lord-feistel/hardware_hacking_lab/images_videos/connection_ISP_atmel.jpeg

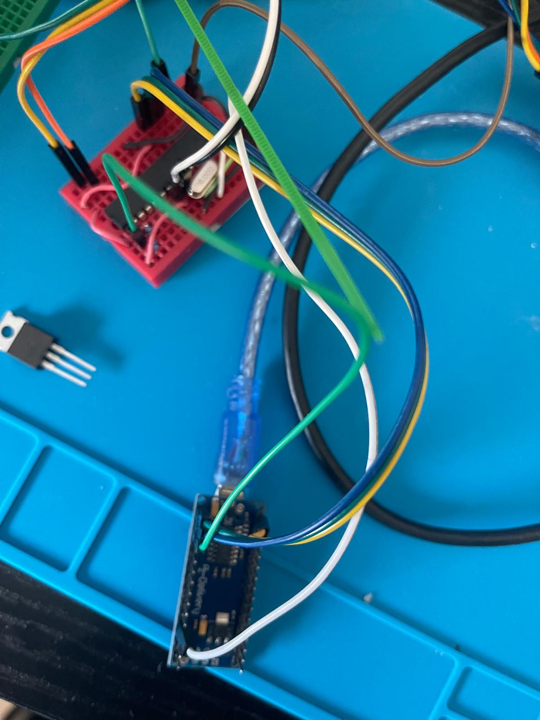
images_videos/connection_ISP_atmel.jpeg
