lord-feistel/hardware_hacking_lab/images_videos/normally_working.PNG

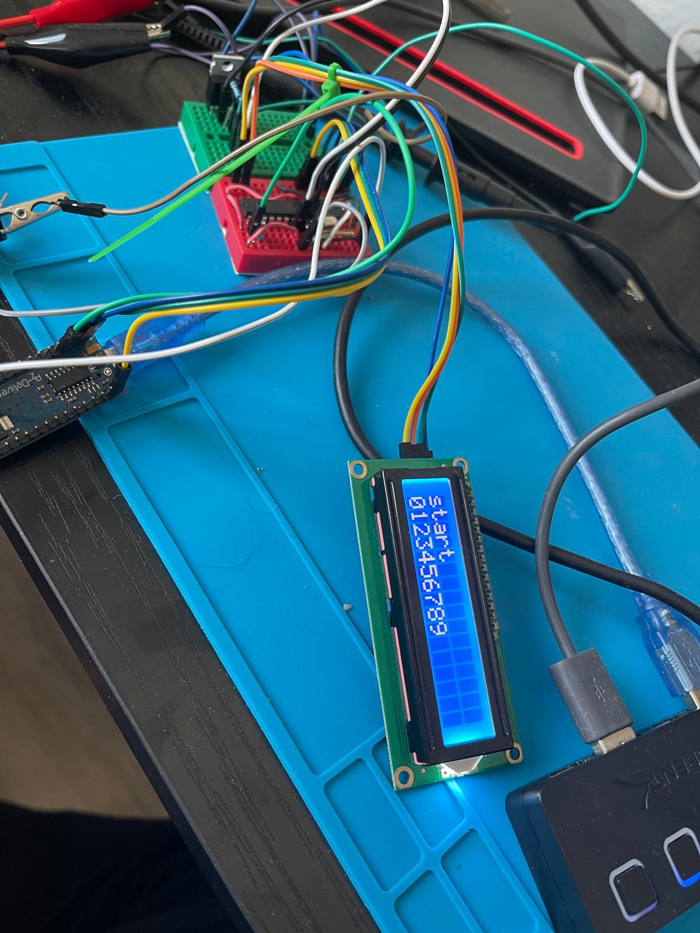
images_videos/normally_working.PNG
