lord-feistel/hardware_hacking_lab/hardware/arduino_glitching/arduino_glitching.kicad_sch

## KiCad design hardware/arduino_glitching/arduino_glitching.kicad_sch (2024-05-03)

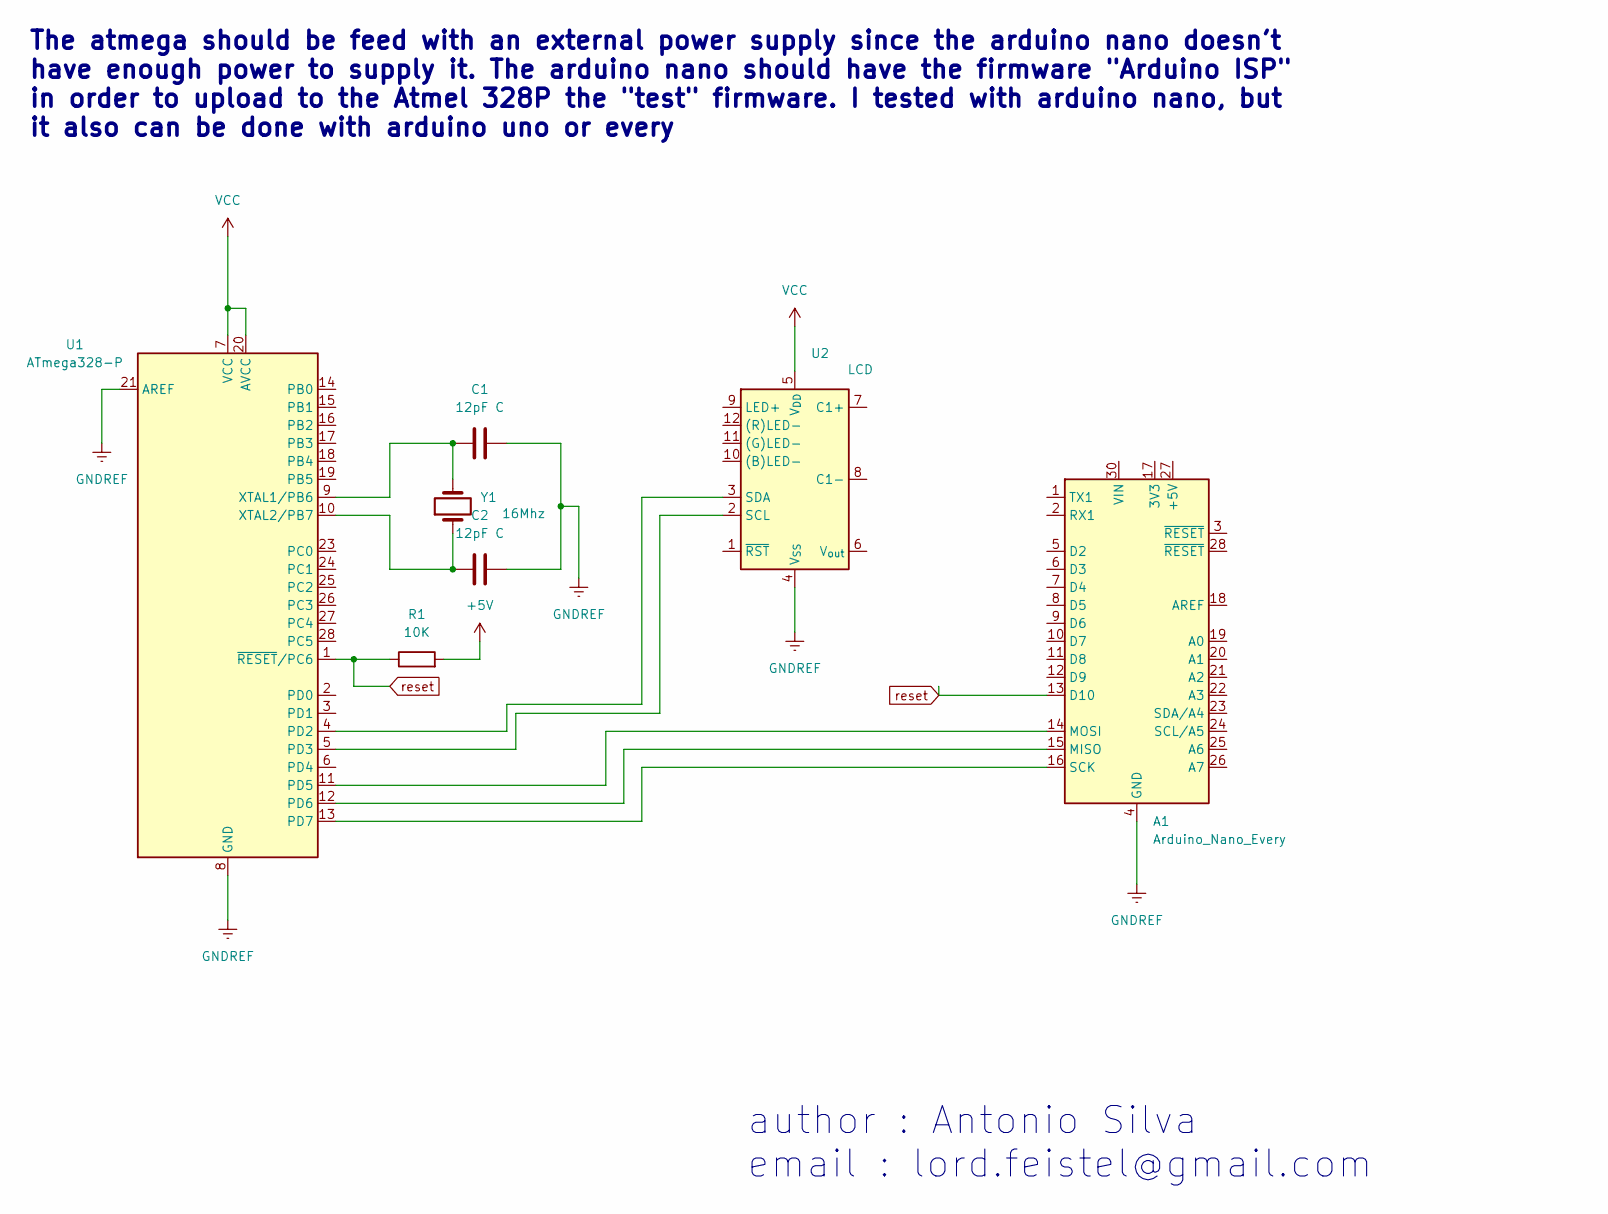
[picture p29: schematic arduino_glitching.kicad_sch]

Parts:
A1: Arduino_Nano_Every; Arduino_Nano
C1, C2: 12pF C
R1: 10K
U1: ATmega328-P; DIP-28_W7.62mm
U2: LCD; NHD-C0220BiZ-FSRGB
Y1: 16Mhz

Connections:
+5V: R1.2
GNDREF: A1.4 (GND), A1.29 (GND), C1.2, C2.2, U1.8 (GND), U1.21 (AREF), U1.22 (GND), U2.4 (V_{SS})
unnamed: A1.14 (MOSI), U1.11 (PD5)
unnamed: A1.15 (MISO), U1.12 (PD6)
unnamed: A1.16 (SCK), U1.13 (PD7)
unnamed: C1.1, U1.9 (XTAL1/PB6), Y1.2
unnamed: C2.1, U1.10 (XTAL2/PB7), Y1.1
unnamed: U1.4 (PD2), U2.3 (SDA)
unnamed: U1.5 (PD3), U2.2 (SCL)
VCC: U1.7 (VCC), U1.20 (AVCC), U2.5 (V_{DD})
reset: A1.13 (D10), R1.1, U1.1 (~RESET/PC6)

Notes on the sheet:
The atmega should be feed with an external power supply since the arduino nano doesn't have enough power to supply it. The arduino nano should have the firmware "Arduino ISP" in order to upload to the Atmel 328P the "test" firmware. I tested with arduino nano, but it also can be done with arduino u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
author : Antonio Silva email : lord.feistel@gmail.com
