lord-feistel/hardware_hacking_lab/hardware/arduino_glitching/arduino_mosfet/arduino_mosfet.kicad_sch

## KiCad design hardware/arduino_glitching/arduino_mosfet/arduino_mosfet.kicad_sch (2024-05-03)

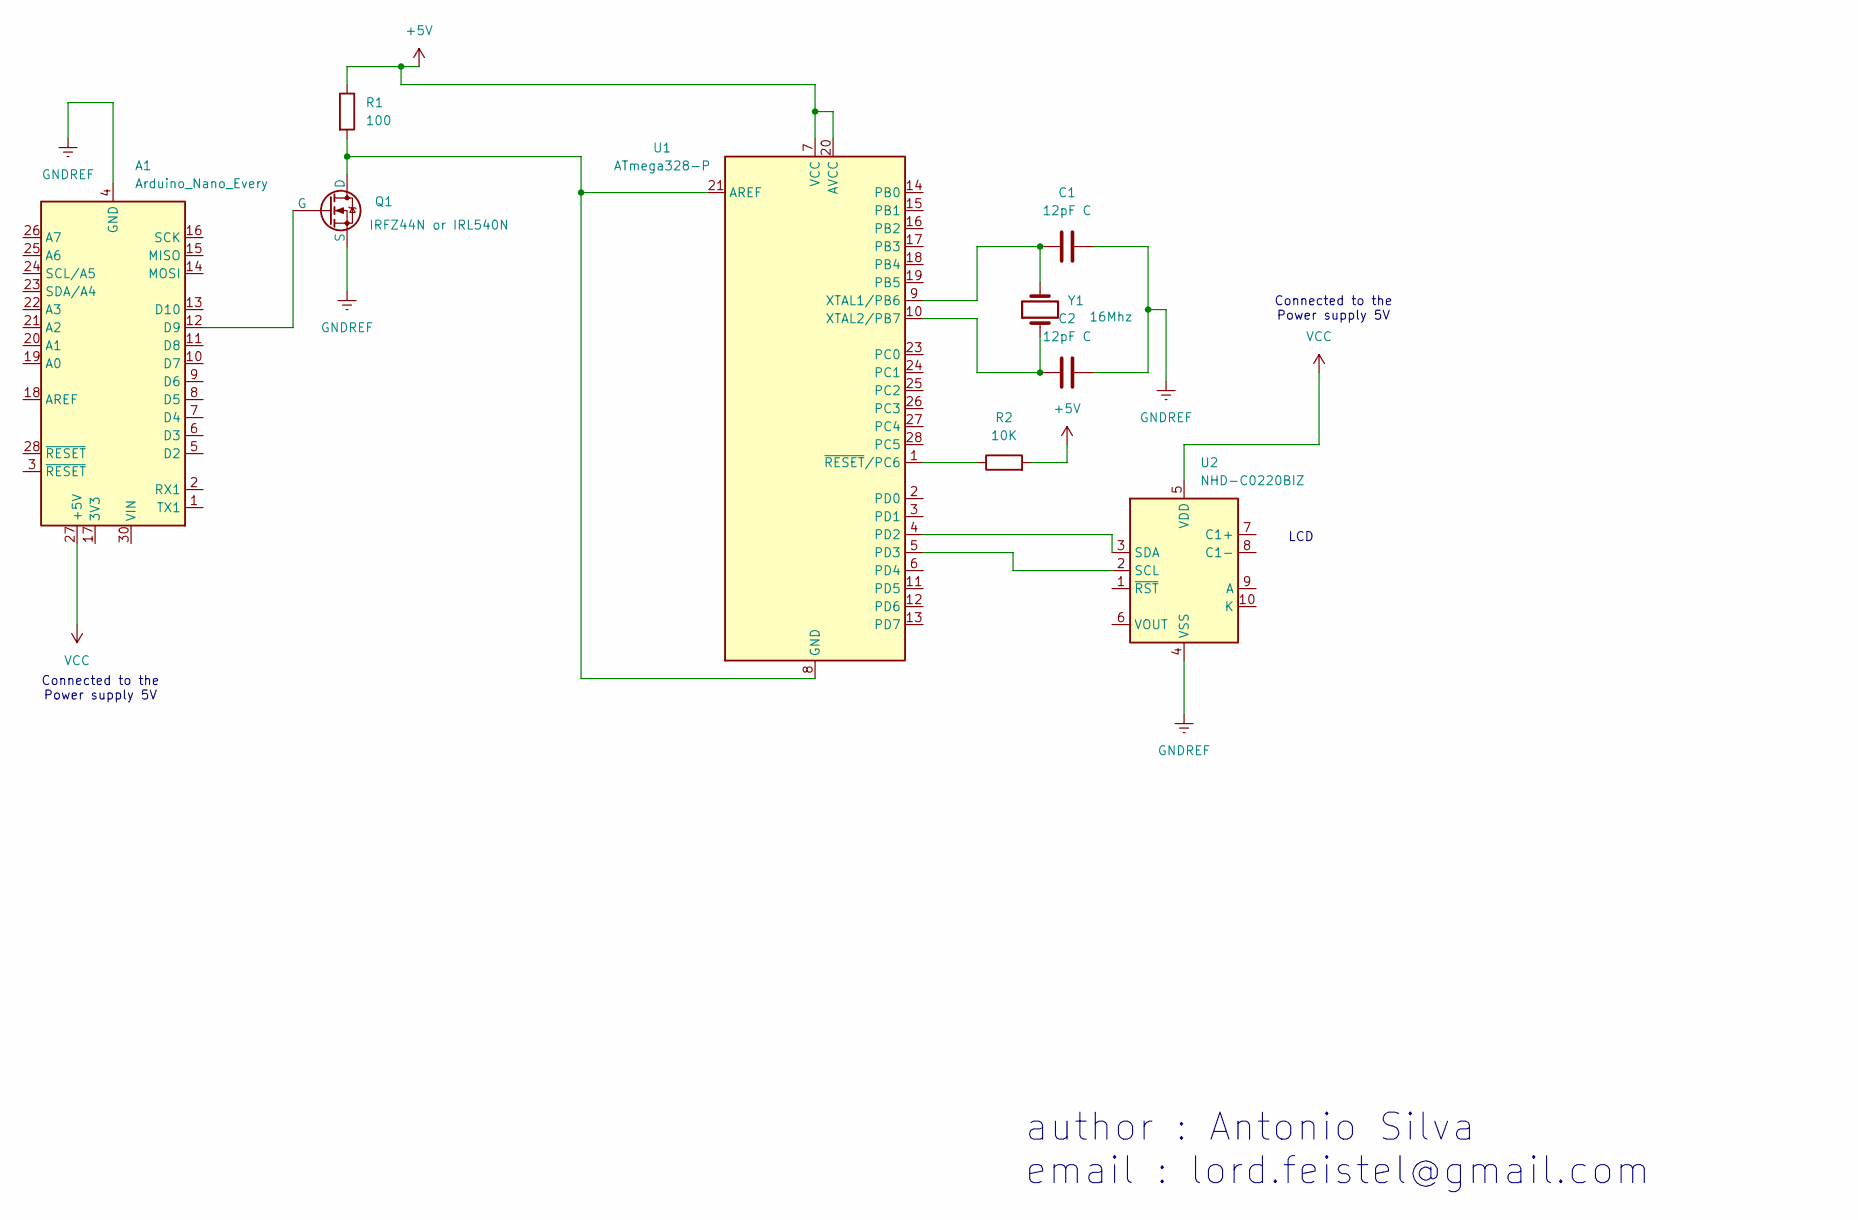
[picture p30: schematic arduino_mosfet.kicad_sch]

Parts:
A1: Arduino_Nano_Every; Arduino_Nano
C1, C2: 12pF C
Q1: IRFZ44N or IRL540N
R1: 100
R2: 10K
U1: ATmega328-P; DIP-28_W7.62mm
U2: NHD-C0220BIZ; NHD-C0220BiZ
Y1: 16Mhz

Connections:
+5V: R1.1, R2.2, U1.7 (VCC), U1.20 (AVCC)
GNDREF: A1.4 (GND), A1.29 (GND), C1.2, C2.2, Q1.3 (S), U2.4 (VSS)
unnamed: A1.12 (D9), Q1.2 (G)
unnamed: C1.1, U1.9 (XTAL1/PB6), Y1.2
unnamed: C2.1, U1.10 (XTAL2/PB7), Y1.1
unnamed: Q1.1 (D), R1.2, U1.8 (GND), U1.21 (AREF), U1.22 (GND)
unnamed: R2.1, U1.1 (~RESET/PC6)
unnamed: U1.4 (PD2), U2.3 (SDA)
unnamed: U1.5 (PD3), U2.2 (SCL)
VCC: A1.27 (+5V), U2.5 (VDD)

Notes on the sheet:
Connected to the Power supply 5V
author : Antonio Silva email : lord.feistel@gmail.com
LCD
